sudochamp/enlarger-timer/src/max7219.h

// 16MHz clock
#define F_CPU 16000000UL

// Outputs, pin definitions
#define PIN_SCK                   PORTB5
#define PIN_MOSI                  PORTB3
#define PIN_SS                    PORTB2

#define ON                        1
#define OFF                       0

#define MAX7219_LOAD1             PORTB |= (1<<PIN_SS)
#define MAX7219_LOAD0             PORTB &= ~(1<<PIN_SS)

#define MAX7219_MODE_DECODE       0x09
#define MAX7219_MODE_INTENSITY    0x0A
#define MAX7219_MODE_SCAN_LIMIT   0x0B
#define MAX7219_MODE_POWER        0x0C
#define MAX7219_MODE_TEST         0x0F
#define MAX7219_MODE_NOOP         0x00

// I only have 3 digits, no point having the
// rest. You could use more though.
#define MAX7219_DIGIT0            0x01
#define MAX7219_DIGIT1            0x02
#define MAX7219_DIGIT2            0x03
#define MAX7219_DIGIT3            0x04

#define MAX7219_CHAR_BLANK        0xF 
#define MAX7219_CHAR_NEGATIVE     0xA 
#define MAX7219_CHAR_DP           0x80

#define DIGITS_IN_USE 4

void spiMasterInit (void);

void spiSendByte (char databyte);

void MAX7219_writeData(char data_register, char data);

void MAX7219_clearDisplay();

void MAX7219_displayNumber(volatile long number) ;
